AG2048/spark_frosh_kit_2t5/imgs/board_previews/board_1_fusion_preview_front.png

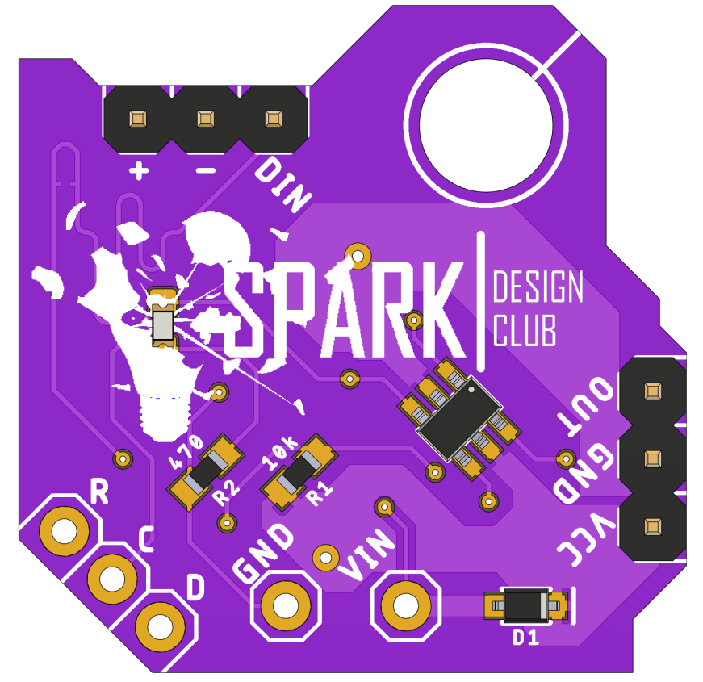
imgs/board_previews/board_1_fusion_preview_front.png
