AG2048/spark_frosh_kit_2t5/imgs/board_previews/board_2_fusion_preview_back.png

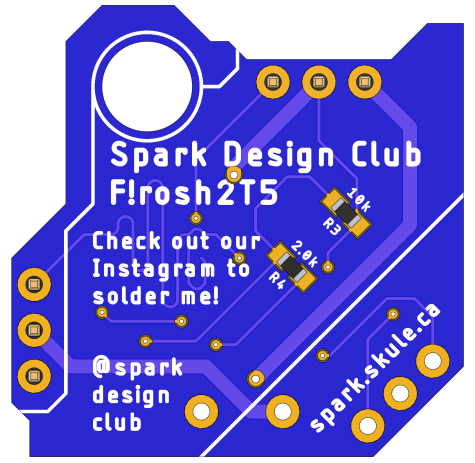
imgs/board_previews/board_2_fusion_preview_back.png
