AG2048/spark_frosh_kit_2t5/imgs/produced_boards/four_boards_pieced_front.png

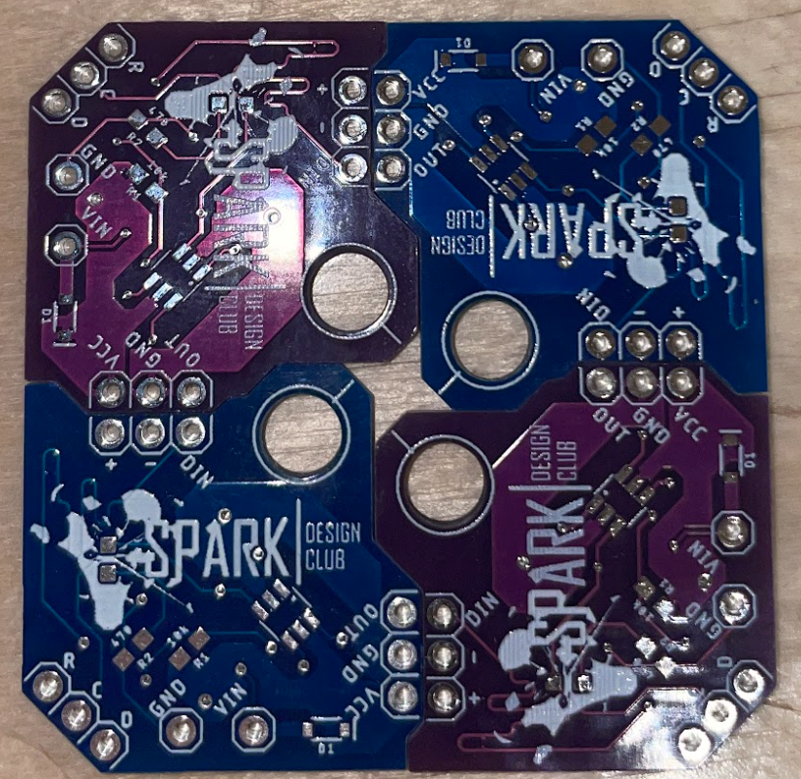
imgs/produced_boards/four_boards_pieced_front.png
