AG2048/spark_frosh_kit_2t5/imgs/produced_boards/assembled_with_stands.JPG

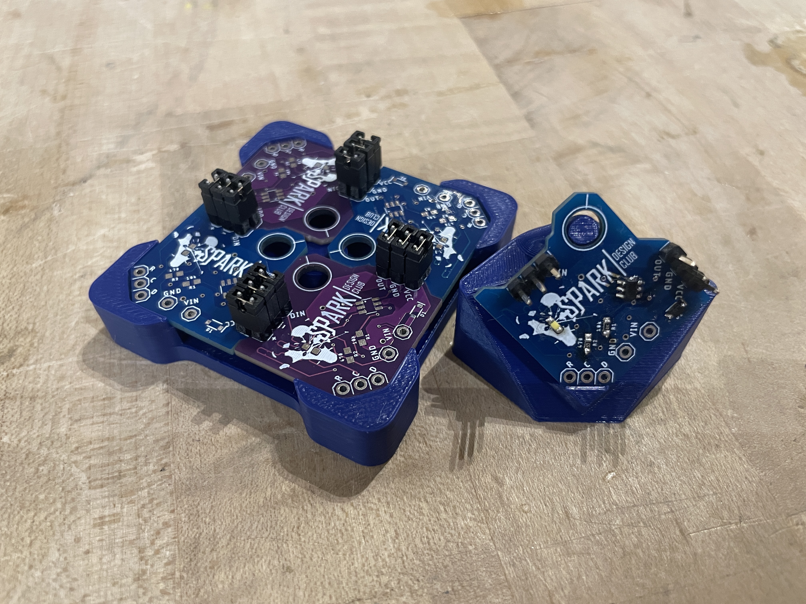
imgs/produced_boards/assembled_with_stands.JPG
