AG2048/spark_frosh_kit_2t5/imgs/produced_boards/sample_assembly.png

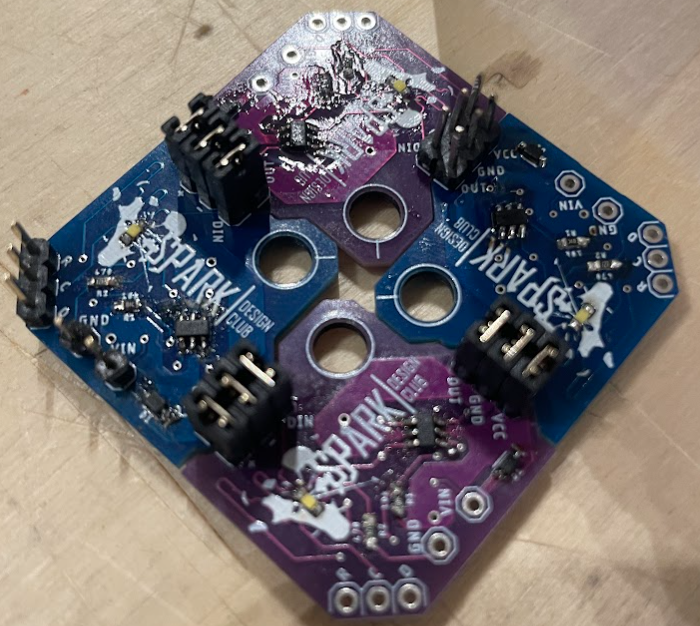
imgs/produced_boards/sample_assembly.png
